InzynierDomu/PhECMeter/src/Calibration_data_memory.cpp

/**
 * @file Linear_function.cpp
 * @author by Szymon Markiewicz (https://github.com/InzynierDomu/)
 * @brief saving and loading calibration data from memory
 * @date 2022-06
 */
#include "Calibration_data_memory.h"

/**
 * @brief save ph calibration data
 * @param points calibration data
 */
void Calibration_data_memory::save_ph_calibration(const Point points[2])
{
  save_calibration(points, 0);
}

/**
 * @brief save ec calibration data
 * @param points calibration data
 */
void Calibration_data_memory::save_ec_calibration(const Point points[2])
{
  save_calibration(points, 4);
}

/**
 * @brief load ph calibration data
 * @param points calibration data to fill
 */
void Calibration_data_memory::load_ph_calibration(Point points[2])
{
  load_calibration(points, 0);
}

/**
 * @brief load ec calibration data
 * @param points calibration data to fill
 */
void Calibration_data_memory::load_ec_calibration(Point points[2])
{
  load_calibration(points, 4);
}

void Calibration_data_memory::save_calibration(const Point points[2], const uint8_t start)
{
  EEPROM.put<double>(sizeof(double) * start, points[0].analog_val);
  EEPROM.put<double>(sizeof(double) * (start + 1), points[0].unit_val);
  EEPROM.put<double>(sizeof(double) * (start + 2), points[1].analog_val);
  EEPROM.put<double>(sizeof(double) * (start + 3), points[1].unit_val);
}

void Calibration_data_memory::load_calibration(Point points[2], const uint8_t start)
{
  double analog_val;
  double unit_val;
  EEPROM.get<double>(sizeof(double) * start, analog_val);
  EEPROM.get<double>(sizeof(double) * (start + 1), unit_val);
  points[0] = Point(analog_val, unit_val);
  EEPROM.get<double>(sizeof(double) * (start + 2), analog_val);
  EEPROM.get<double>(sizeof(double) * (start + 3), unit_val);
  points[1] = Point(analog_val, unit_val);
}
